TheSuperPixel/chess_robot_with_fpga/code/rtl/ddr3_rw.v

// Descriptions:        ddr3控制器读写模块

module ddr3_rw(          
    input           ui_clk               ,  //用户时钟
    input           ui_clk_sync_rst      ,  //复位,高有效
    input           init_calib_complete  ,  //DDR3初始化完成
    input           app_rdy              ,  //MIG IP核空闲
    input           app_wdf_rdy          ,  //MIG写FIFO空闲
    input           app_rd_data_valid    ,  //读数据有效
    input   [9:0]   wfifo_rcount         ,  //写端口FIFO中的数据量
    input   [9:0]   rfifo_wcount         ,  //读端口FIFO中的数据量
    input           rd_load              ,  //输出源更新信号
    input           wr_load              ,  //输入源更新信号
    input   [27:0]  app_addr_rd_min      ,  //读DDR3的起始地址
    input   [27:0]  app_addr_rd_max      ,  //读DDR3的结束地址
    input   [7:0]   rd_bust_len          ,  //从DDR3中读数据时的突发长度
    input   [27:0]  app_addr_wr_min      ,  //写DDR3的起始地址
    input   [27:0]  app_addr_wr_max      ,  //写DDR3的结束地址
    input   [7:0]   wr_bust_len          ,  //从DDR3中写数据时的突发长度

    input           ddr3_read_valid      ,  //DDR3 读使能   
    input           ddr3_pingpang_en     ,  //DDR3 乒乓操作使能          
    output          rfifo_wren           ,  //从ddr3读出数据的有效使能 
    output  [27:0]  app_addr             ,  //DDR3地址                 
    output          app_en               ,  //MIG IP核操作使能
    output          app_wdf_wren         ,  //用户写使能   
    output          app_wdf_end          ,  //突发写当前时钟最后一个数据 
    output  [2:0]   app_cmd                 //MIG IP核操作命令，读或者写       
    );
    
//localparam 
localparam IDLE        = 4'b0001;   //空闲状态
localparam DDR3_DONE   = 4'b0010;   //DDR3初始化完成状态
localparam WRITE       = 4'b0100;   //读FIFO保持状态
localparam READ        = 4'b1000;   //写FIFO保持状态

//reg define
reg    [27:0] app_addr_rd;          //DDR3读地址
reg    [27:0] app_addr_wr;          //DDR3写地址
reg    [3:0]  state_cnt;            //状态计数器
reg    [23:0] rd_addr_cnt;          //用户读地址计数
reg    [23:0] wr_addr_cnt;          //用户写地址计数  
reg    [10:0] raddr_rst_h_cnt;      //输出源的帧复位脉冲进行计数 
reg    [27:0] app_addr_rd_min_a;    //读DDR3的起始地址
reg    [27:0] app_addr_rd_max_a;    //读DDR3的结束地址
reg    [7:0]  rd_bust_len_a;        //从DDR3中读数据时的突发长度
reg    [27:0] app_addr_wr_min_a;    //写DDR3的起始地址
reg    [27:0] app_addr_wr_max_a;    //写DDR3的结束地址
reg    [7:0]  wr_bust_len_a;        //从DDR3中写数据时的突发长度
reg           rd_load_d0;
reg           rd_load_d1;
reg           raddr_rst_h;          //输出源的帧复位脉冲
reg           wr_load_d0;
reg           wr_load_d1;
reg           wr_rst;               //输入源帧复位标志
reg           rd_rst;               //输出源帧复位标志
reg           raddr_page;           //ddr3读地址切换信号
reg           waddr_page;           //ddr3写地址切换信号
reg           wr_end;               //一次突发写结束信号
reg           rd_end;               //一次读发写结束信号 
reg [27:0]    app_addr;  

//wire define
wire          rst_n;

 //*****************************************************
//**                    main code
//***************************************************** 

//将数据有效信号赋给wfifo写使能
assign rfifo_wren =  app_rd_data_valid;

assign rst_n = ~ui_clk_sync_rst;

//在写状态MIG空闲且写有效,或者在读状态MIG空闲，此时使能信号为高，其他情况为低
assign app_en = ((state_cnt == WRITE && (app_rdy && app_wdf_rdy))
                ||(state_cnt == READ && app_rdy)) ? 1'b1:1'b0;
                
//在写状态,MIG空闲且写有效，此时拉高写使能
assign app_wdf_wren = (state_cnt == WRITE && (app_rdy && app_wdf_rdy)) ? 1'b1:1'b0;

//由于我们DDR3芯片时钟和用户时钟的分频选择4:1，突发长度为8，故两个信号相同
assign app_wdf_end = app_wdf_wren; 

//处于读的时候命令值为1，其他时候命令值为0
assign app_cmd = (state_cnt == READ) ? 3'd1 :3'd0; 

//将数据读写地址赋给ddr地址
always @(*) begin
    if(~rst_n)
        app_addr <= 0;
    else if(state_cnt == READ )
        if(ddr3_pingpang_en)
            app_addr <= {2'b0,raddr_page,app_addr_rd[24:0]};
        else 
            app_addr <= {3'b0,app_addr_rd[24:0]};            
    else if(ddr3_pingpang_en)
        app_addr <= {2'b0,waddr_page,app_addr_wr[24:0]};
    else
        app_addr <= {3'b0,app_addr_wr[24:0]};        
end  

//对信号进行打拍处理
always @(posedge ui_clk or negedge rst_n)  begin
    if(~rst_n)begin
        rd_load_d0 <= 0;
        rd_load_d1 <= 0; 
        wr_load_d0 <= 0; 
        wr_load_d1 <= 0;                    
    end   
    else begin
        rd_load_d0 <= rd_load;
        rd_load_d1 <= rd_load_d0;  
        wr_load_d0 <= wr_load; 
        wr_load_d1 <= wr_load_d0;                
    end    
end 

//对异步信号进行打拍处理
always @(posedge ui_clk or negedge rst_n)  begin
    if(~rst_n)begin
        app_addr_rd_min_a <= 0;
        app_addr_rd_max_a <= 0; 
        rd_bust_len_a <= 0; 
        app_addr_wr_min_a <= 0;  
        app_addr_wr_max_a <= 0; 
        wr_bust_len_a <= 0;                            
    end   
    else begin
        app_addr_rd_min_a <= app_addr_rd_min;
        app_addr_rd_max_a <= app_addr_rd_max; 
        rd_bust_len_a <= rd_bust_len; 
        app_addr_wr_min_a <= app_addr_wr_min;  
        app_addr_wr_max_a <= app_addr_wr_max; 
        wr_bust_len_a <= wr_bust_len;                    
    end    
end 
 
//对输入源做个帧复位标志
always @(posedge ui_clk or negedge rst_n)  begin
    if(~rst_n)
        wr_rst <= 0;                
    else if(wr_load_d0 && !wr_load_d1)
        wr_rst <= 1;               
    else
        wr_rst <= 0;           
end
 
//对输出源做个帧复位标志 
always @(posedge ui_clk or negedge rst_n)  begin
    if(~rst_n)
        rd_rst <= 0;                
    else if(rd_load_d0 && !rd_load_d1)
        rd_rst <= 1;               
    else
        rd_rst <= 0;           
end

//对输出源的读地址做个帧复位脉冲 
always @(posedge ui_clk or negedge rst_n)  begin
    if(~rst_n)
        raddr_rst_h <= 1'b0;
    else if(rd_load_d0 && !rd_load_d1)
        raddr_rst_h <= 1'b1;
    else if(app_addr_rd == app_addr_rd_min_a)   
        raddr_rst_h <= 1'b0;
    else
        raddr_rst_h <= raddr_rst_h;              
end 

//对输出源的帧复位脉冲进行计数 
always @(posedge ui_clk or negedge rst_n)  begin
    if(~rst_n)
        raddr_rst_h_cnt <= 11'b0;
    else if(raddr_rst_h)
        raddr_rst_h_cnt <= raddr_rst_h_cnt + 1'b1;
    else
        raddr_rst_h_cnt <= 11'b0;            
end 

//对输出源帧的读地址高位切换
always @(posedge ui_clk or negedge rst_n)  begin
    if(~rst_n)
        raddr_page <= 1'b0;
    else if( rd_end)
        raddr_page <= ~waddr_page;         
    else
        raddr_page <= raddr_page;           
end 
  
//对输入源帧的写地址高位切换
always @(posedge ui_clk or negedge rst_n)  begin
    if(~rst_n)
        waddr_page <= 1'b1;
    else if( wr_end)
        waddr_page <= ~waddr_page ;         
    else
        waddr_page <= waddr_page;           
end   
   
//DDR3读写逻辑实现
always @(posedge ui_clk or negedge rst_n) begin
    if(~rst_n) begin 
        state_cnt    <= IDLE;              
        wr_addr_cnt  <= 24'd0;      
        rd_addr_cnt  <= 24'd0;       
        app_addr_wr  <= app_addr_wr_min_a;   
        app_addr_rd  <= app_addr_rd_min_a; 
        wr_end       <= 1'b0;
        rd_end       <= 1'b0;       
    end
    else begin
        case(state_cnt)
            IDLE:begin
                if(init_calib_complete)
                    state_cnt <= DDR3_DONE ;
                else
                    state_cnt <= IDLE;
            end
            DDR3_DONE:begin
                if(wr_rst)begin   //当帧复位到来时，对寄存器进行复位
                    state_cnt <= DDR3_DONE;
                    wr_addr_cnt  <= 24'd0;	
                    app_addr_wr <= app_addr_wr_min_a;					
			    end    //当读到结束地址对寄存器复位
                else if(app_addr_rd >= app_addr_rd_max_a - 4'd8)begin  
                        state_cnt <= DDR3_DONE;
                        rd_addr_cnt  <= 24'd0;      
                        app_addr_rd <= app_addr_rd_min_a; 
                        rd_end <= 1'b1;
                end	   //当写到结束地址对寄存器复位
                else if(app_addr_wr >= app_addr_wr_max_a - 4'd8)begin  
                        state_cnt <= DDR3_DONE;
                        wr_addr_cnt  <= 24'd0;      
                        app_addr_wr <= app_addr_wr_min_a; 
                        wr_end <= 1'b1;
                end	                		    
                else if(wfifo_rcount >= wr_bust_len_a - 2'd2)begin  
                    state_cnt <= WRITE;              //跳到写操作
                    wr_addr_cnt  <= 24'd0;                       
                    app_addr_wr <= app_addr_wr;      //写地址保持不变
                end
                else if(raddr_rst_h)begin           //当帧复位到来时，对寄存器进行复位 
                    if(raddr_rst_h_cnt >= 1000 && ddr3_read_valid)begin  
                        state_cnt <= READ;         //保证读fifo在复位时不回写入数据
                        rd_addr_cnt  <= 24'd0;      
                        app_addr_rd <= app_addr_rd_min_a; 
                    end
                    else begin
                        state_cnt <= DDR3_DONE;
                        rd_addr_cnt  <= 24'd0;      
                        app_addr_rd <= app_addr_rd;                                
                    end                                
                end //当rfifo存储数据少于一次突发长度时,并且ddr已经写入了1帧数据
                else if(rfifo_wcount < rd_bust_len_a && ddr3_read_valid )begin  
                    state_cnt <= READ;                              //跳到读操作
                    rd_addr_cnt <= 24'd0;
                    app_addr_rd <= app_addr_rd;      //读地址保持不变
                end
                else begin
                    state_cnt <= state_cnt;   
                    wr_addr_cnt  <= 24'd0;      
                    rd_addr_cnt  <= 24'd0;  
                    rd_end <= 1'b0;   
                    wr_end <= 1'b0;                                       
                end
            end    
            WRITE:   begin 
                if((wr_addr_cnt == (wr_bust_len_a - 1'b1)) && 
                   (app_rdy && app_wdf_rdy))begin    //写到设定的长度跳到等待状态                  
                    state_cnt    <= DDR3_DONE;       //写到设定的长度跳到等待状态               
                    app_addr_wr <= app_addr_wr + 4'd8;  //一次性写进8个数，故加8
                end       
                else if(app_rdy && app_wdf_rdy)begin   //写条件满足
                    wr_addr_cnt  <= wr_addr_cnt + 1'b1;//写地址计数器自加
                    app_addr_wr  <= app_addr_wr + 4'd8;   //一次性写进8个数，故加8
                end
                else begin                             //写条件不满足，保持当前值     
                    wr_addr_cnt  <= wr_addr_cnt;
                    app_addr_wr  <= app_addr_wr; 
                end
            end
            READ:begin                      //读到设定的地址长度    
                if((rd_addr_cnt == (rd_bust_len_a - 1'b1)) && app_rdy)begin
                    state_cnt   <= DDR3_DONE;          //则跳到空闲状态 
                    app_addr_rd <= app_addr_rd + 4'd8;
                end       
                else if(app_rdy)begin               //若MIG已经准备好,则开始读
                    rd_addr_cnt <= rd_addr_cnt + 1'b1; //用户地址计数器每次加一
                    app_addr_rd <= app_addr_rd + 4'd8; //一次性读出8个数,DDR3地址加8
                end
                else begin                         //若MIG没准备好,则保持原值
                    rd_addr_cnt <= rd_addr_cnt;
                    app_addr_rd <= app_addr_rd; 
                end
            end             
            default:begin
                state_cnt    <= IDLE;
                wr_addr_cnt  <= 24'd0;
                rd_addr_cnt  <= 24'd0;
            end
        endcase
    end
end                          

endmodule
