TheSuperPixel/chess_robot_with_fpga/code/rtl3/line_shift_ram_8bit.v

module line_shift_ram_8bit(
    input          clock,   
    input          clken,
    input          pre_frame_href,
    
    input   [7:0]  shiftin,  
    output  [7:0]  taps0x,   
    output  [7:0]  taps1x    
);

//reg define
reg  [2:0]  clken_dly;
reg  [9:0]  ram_rd_addr;
reg  [9:0]  ram_rd_addr_d0;
reg  [9:0]  ram_rd_addr_d1;
reg  [7:0]  shiftin_d0;
reg  [7:0]  shiftin_d1;
reg  [7:0]  shiftin_d2;
reg  [7:0]  taps0x_d0;

//*****************************************************
//**                    main code
//*****************************************************

//在数据来到时，ram地址累加
always@(posedge clock)begin
    if(pre_frame_href)
        if(clken)
            ram_rd_addr <= ram_rd_addr + 1 ;
        else
            ram_rd_addr <= ram_rd_addr ;
    else
        ram_rd_addr <= 0 ;
end

//时钟使能信号延迟三拍
always@(posedge clock) begin
    clken_dly <= { clken_dly[1:0] , clken };
end


//将ram地址延迟二拍
always@(posedge clock ) begin
    ram_rd_addr_d0 <= ram_rd_addr;
    ram_rd_addr_d1 <= ram_rd_addr_d0;
end

//输入数据延迟三拍
always@(posedge clock)begin
    shiftin_d0 <= shiftin;
    shiftin_d1 <= shiftin_d0;
    shiftin_d2 <= shiftin_d1;
end

//用于存储前一行图像的RAM
blk_mem_gen_0  u_ram_1024x8_0(    
    .clka   (clock), 
    .wea   (clken_dly[2]),    //在延迟的第三个时钟周期，当前行的数据写入RAM0
    .addra (ram_rd_addr_d1),
    .dina  (shiftin_d2),
    .clkb  (clock),
    .addrb (ram_rd_addr),
    .doutb (taps0x)           //延迟一个时钟周期，输出RAM0中前一行图像的数据
); 

//寄存一次前一行图像的数据
always@(posedge clock ) begin
    taps0x_d0 <= taps0x;
end

blk_mem_gen_0  u_ram_1024x8_1(    
    .clka   (clock),           
    .wea   (clken_dly[1]),    //在延迟的第二个时钟周期，将前一行图像的数据写入RAM1
    .addra (ram_rd_addr_d0),
    .dina  (taps0x_d0),
    .clkb  (clock),
    .addrb (ram_rd_addr),
    .doutb (taps1x)           //延迟一个时钟周期，输出RAM1中前前一行图像的数据
); 

endmodule 
